joshua691/Blue-LED-Cube/images and gifs/Bread Board Layout.jpg

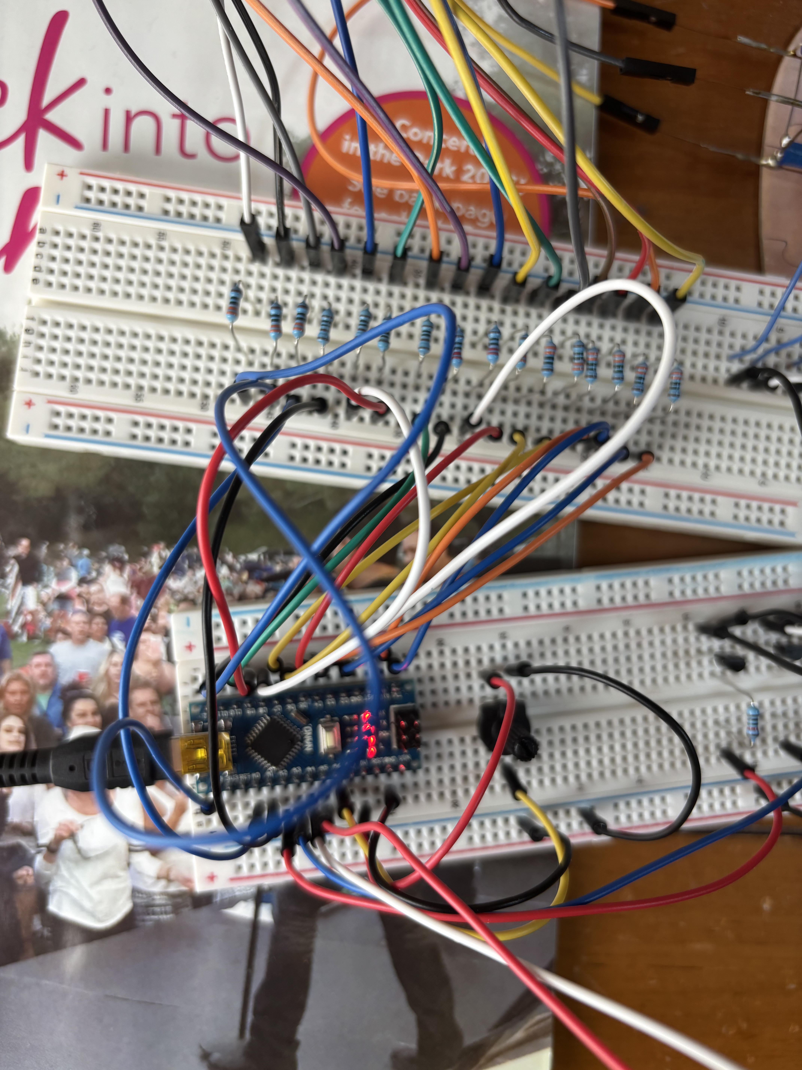
images and gifs/Bread Board Layout.jpg
